lucadentella/espThrottle/Arduino/espThrottle/Icons.h

static uint8_t battery[33] = {
    0xff, 0xff, 0xe0, 
    0x80, 0x00, 0x20, 
    0x80, 0x00, 0x20, 
    0x80, 0x00, 0x38, 
    0x80, 0x00, 0x38, 
    0x80, 0x00, 0x38, 
    0x80, 0x00, 0x38, 
    0x80, 0x00, 0x38, 
    0x80, 0x00, 0x20, 
    0x80, 0x00, 0x20, 
    0xff, 0xff, 0xe0
};

static uint8_t batterycharging[33] = {
    0xff, 0xff, 0xe0, 
    0x80, 0x00, 0x20, 
    0x81, 0x00, 0x20, 
    0x87, 0x80, 0x38, 
    0x9f, 0xc0, 0x38, 
    0xbf, 0xff, 0xb8, 
    0x80, 0x7f, 0x38, 
    0x80, 0x3c, 0x38, 
    0x80, 0x10, 0x20, 
    0x80, 0x00, 0x20, 
    0xff, 0xff, 0xe0
};

static uint8_t arrowleft[45] = {
    0x00, 0x20, 0x00, 
    0x00, 0x30, 0x00, 
    0x00, 0x38, 0x00, 
    0x00, 0x3c, 0x00, 
    0x00, 0x3e, 0x00, 
    0xff, 0xff, 0x00, 
    0xff, 0xff, 0x80, 
    0xff, 0xff, 0xc0, 
    0xff, 0xff, 0x80, 
    0xff, 0xff, 0x00, 
    0x00, 0x3e, 0x00, 
    0x00, 0x3c, 0x00, 
    0x00, 0x38, 0x00, 
    0x00, 0x30, 0x00, 
    0x00, 0x20, 0x00
};

static uint8_t arrowright[45] = {
    0x01, 0x00, 0x00, 
    0x03, 0x00, 0x00, 
    0x07, 0x00, 0x00, 
    0x0f, 0x00, 0x00, 
    0x1f, 0x00, 0x00, 
    0x3f, 0xff, 0xc0, 
    0x7f, 0xff, 0xc0, 
    0xff, 0xff, 0xc0, 
    0x7f, 0xff, 0xc0, 
    0x3f, 0xff, 0xc0, 
    0x1f, 0x00, 0x00, 
    0x0f, 0x00, 0x00, 
    0x07, 0x00, 0x00, 
    0x03, 0x00, 0x00, 
    0x01, 0x00, 0x00
};

static uint8_t wifisetup[1300] = {
    0x00, 0x00, 0x00, 0x00, 0x00, 0x00, 0x00, 0x00, 0x00, 0x00, 0x00, 0x00, 0x00, 
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
    0x00, 0x1f, 0x00, 0x7f, 0xfe, 0x00, 0x00, 0x03, 0xff, 0xe0, 0x0f, 0x00, 0x00, 
    0x00, 0x1e, 0x00, 0xff, 0xf0, 0x00, 0x00, 0x00, 0xff, 0xf8, 0x0f, 0x80, 0x00, 
    0x00, 0x1e, 0x01, 0xff, 0xc0, 0x00, 0x00, 0x00, 0x3f, 0xfc, 0x07, 0x80, 0x00, 
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
};
